padinadrian/n64_dualshock/docs/Captures/ps2_analog_poll.png

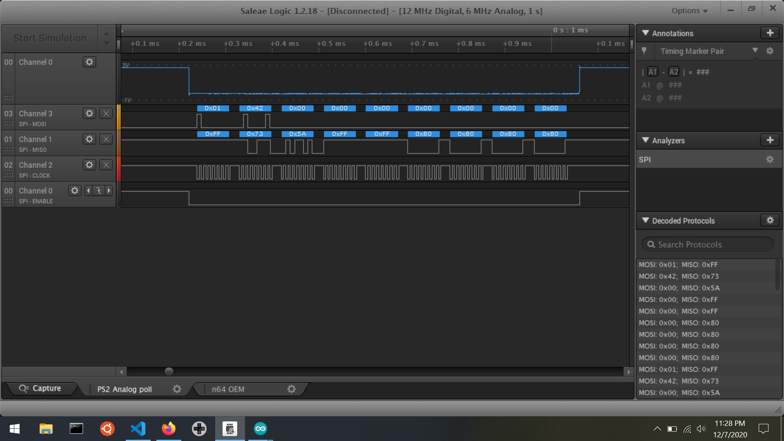
docs/Captures/ps2_analog_poll.png
