padinadrian/n64_dualshock/trinketPS2/trinketloader_modified/trinketloader/images.cpp

#include "optiLoader.h"

const image_t PROGMEM image_328 = {
    {"blankfull.hex"},
    {"attiny85"},
    0x930B,            /* Signature bytes for attimny85 */
    {0, 0xF1, 0xD5, 0x06},            // pre program fuses (prot/lock, low, high, ext)
    {0, 0, 0, 0},            // post program fuses
    {0x3F, 0xFF, 0xFF, 0x07},           // fuse mask
    8192,     // size of chip flash in bytes
    64,   // size in bytes of flash page
    {
":100000005FCA5FCA5FCA5FCA5FCA5FCA5FCA5FCAA8\n"
":10001000FFFFFFFFFFFFFFFFFFFFFFFFFFFFFFFFF0\n"
":10002000FFFFFFFFFFFFFFFFFFFFFFFFFFFFFFFFE0\n"
":10003000FFFFFFFFFFFFFFFFFFFFFFFFFFFFFFFFD0\n"
":1014C00033C060C08CC05EC05DC05CC05BC05AC031\n"
":1014D00059C058C057C056C055C054C053C004036B\n"
":1014E0000904120341006400610066007200750087\n"
":1014F0006900740010035400720069006E006B00F4\n"
":101500006500740012011001FF00000881179F0C94\n"
":1015100005010102000109021200010100803209E7\n"
":10152000040000000000000011241FBECFE5D2E03F\n"
":10153000DEBFCDBF84B7877F84BF88E10FB6F89444\n"
":1015400081BD11BC0FBE81E090E020E80FB6F89499\n"
":1015500026BD86BD0FBE0AEA0F9310E0A0E6B0E0FC\n"
":10156000EAEEFFE102C005900D92A236B107D9F76D\n"
":1015700011E0A2E6B0E001C01D92A832B107E1F788\n"
":10158000EED331C59DCFA82FB92F80E090E041E088\n"
":1015900050EA609530E009C02D9182279795879594\n"
":1015A00010F084279527305EC8F36F5FA8F3089585\n"
":1015B000EADF8D939D930895A6E088279927AA9541\n"
":1015C00069F00197E1F3B399FCCFB39BFECF81E0C3\n"
":1015D0009927A6B3019611F0A871D9F70895CF9372\n"
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
":101F300081E090E020E80FB6F89426BD86BD0FBE84\n"
":101F4000BECAE0E0F0E083E080935700E89510928D\n"
":101F5000710010927000D1CFFF920F931F93CF9317\n"
":101F6000DF9380E090E020E80FB6F89426BD86BDB0\n"
":101F70000FBE80E8F82E00E0C0E0D0E0102F1F0D6B\n"
":101F800011BF1ADB29E0843392070CF0102FF6946E\n"
":101F90002196C830D10511F0012FF0CF115011BF9B\n"
":101FA0001F5F012FEC0110C007DB8453994097FF9E\n"
":101FB00003C0909581959F4F8C179D0714F401B72E\n"
":101FC000EC0181B78F5F81BF21B730E0812F90E0B6\n"
":101FD00001968217930744F701BFDF91CF911F91BC\n"
":0C1FE0000F91FF900895F894FFCF5AFF76\n"
":00000001FF\n"
    }
};


/*
 * Table of defined images
 */
const image_t *images[] = {
  &image_328,
};

uint8_t NUMIMAGES = sizeof(images)/sizeof(images[0]);
