padinadrian/n64_dualshock/trinketPS2/trinketloader_skippow25/trinketloader/images.cpp

#include "optiLoader.h"

const image_t PROGMEM image_328 = {
    {"flashme_lv.skippow25.hex"},
    {"attiny85"},
    0x930B,				/* Signature bytes for attimny85 */
    {0, 0xF1, 0xD5, 0x06},            // pre program fuses (prot/lock, low, high, ext)
    {0, 0, 0, 0},            // post program fuses
    {0x3F, 0xFF, 0xFF, 0x07},           // fuse mask
    8192,     // size of chip flash in bytes
    64,   // size in bytes of flash page
    {
":100000005FCA5FCA5FCA5FCA5FCA5FCA5FCA5FCAA8\n"
":10001000FFFFFFFFFFFFFFFFFFFFFFFFFFFFFFFFF0\n"
":10002000FFFFFFFFFFFFFFFFFFFFFFFFFFFFFFFFE0\n"
":10003000FFFFFFFFFFFFFFFFFFFFFFFFFFFFFFFFD0\n"
":1014C00033C064C090C062C061C060C05FC05EC015\n"
":1014D0005DC05CC05BC05AC059C058C057C004034F\n"
":1014E0000904120341006400610066007200750087\n"
":1014F0006900740010035400720069006E006B00F4\n"
":101500006500740012011001FF00000881179F0C94\n"
":1015100005010102000109021200010100803209E7\n"
":10152000040000000000000011241FBECFE5D2E03F\n"
":10153000DEBFCDBF34B714BE88E10FB6F89481BDCD\n"
":1015400011BC0FBE81E090E020E80FB6F89426BDF4\n"
":1015500086BD0FBE832F857011F0232EB0CF0AEA0F\n"
":101560000F9310E0A0E6B0E0E4EEFFE102C00590CA\n"
":101570000D92A236B107D9F711E0A2E6B0E001C0A2\n"
":101580001D92A832B107E1F7EED32AC599CFA82F53\n"
":10159000B92F80E090E041E050EA609530E009C06A\n"
":1015A0002D9182279795879510F084279527305E97\n"
":1015B000C8F36F5FA8F30895EADF8D939D930895B4\n"
":1015C000A6E088279927AA9569F00197E1F3B399D6\n"
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
":101F30000FB6F89426BD86BD0FBEC1CAE0E0F0E042\n"
":101F400083E080935700E895109271001092700022\n"
":101F5000D1CFFF920F931F93CF93DF9380E090E058\n"
":101F600020E80FB6F89426BD86BD0FBE80E8F82E97\n"
":101F700000E0C0E0D0E0102F1F0D11BF21DB29E0F1\n"
":101F8000843392070CF0102FF6942196C830D105B7\n"
":101F900011F0012FF0CF115011BF1F5F012FEC0185\n"
":101FA00010C00EDB8453994097FF03C09095819534\n"
":101FB0009F4F8C179D0714F401B7EC0181B78F5F19\n"
":101FC00081BF21B730E0812F90E0019682179307FF\n"
":101FD00044F701BFDF91CF911F910F91FF900895BA\n"
":061FE000F894FFCF5AFF48\n"
":00000001FF\n"
    }
};


/*
 * Table of defined images
 */
const image_t *images[] = {
  &image_328,
};

uint8_t NUMIMAGES = sizeof(images)/sizeof(images[0]);
